telzo2000/cool838ax/img/img00001.jpg

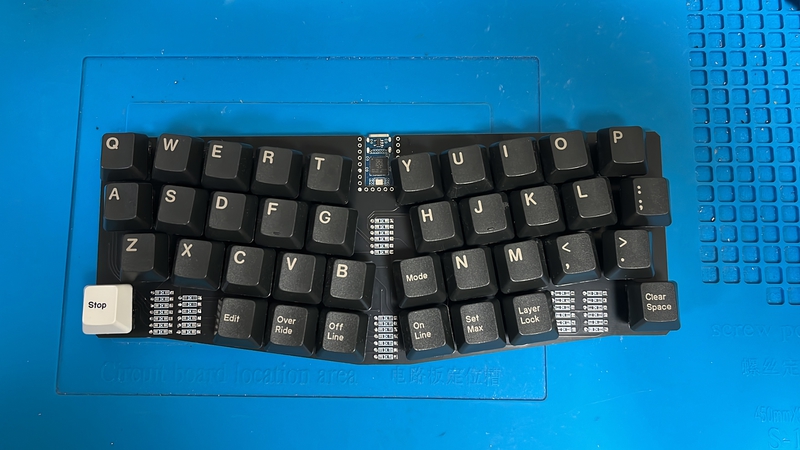
img/img00001.jpg
