telzo2000/cool838ax/img/IMG_1909.jpg

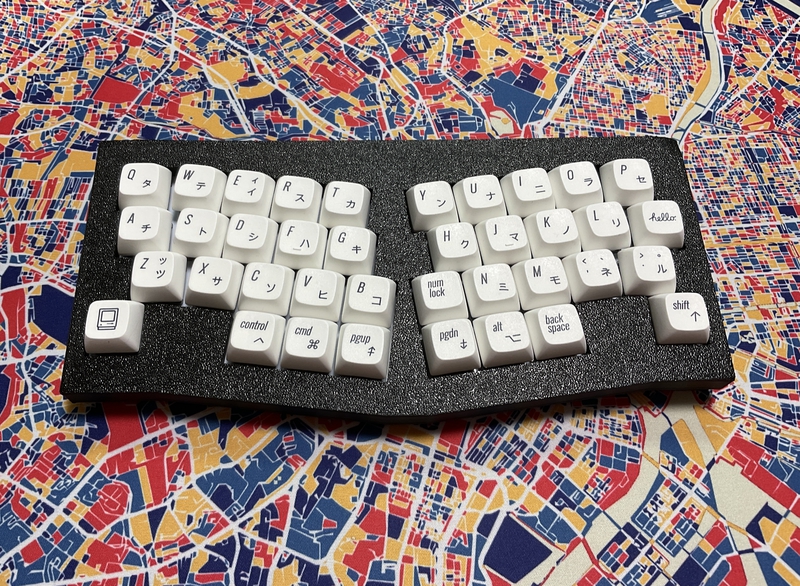
img/IMG_1909.jpg
