telzo2000/cool838ax/img/IMG_1910.jpg

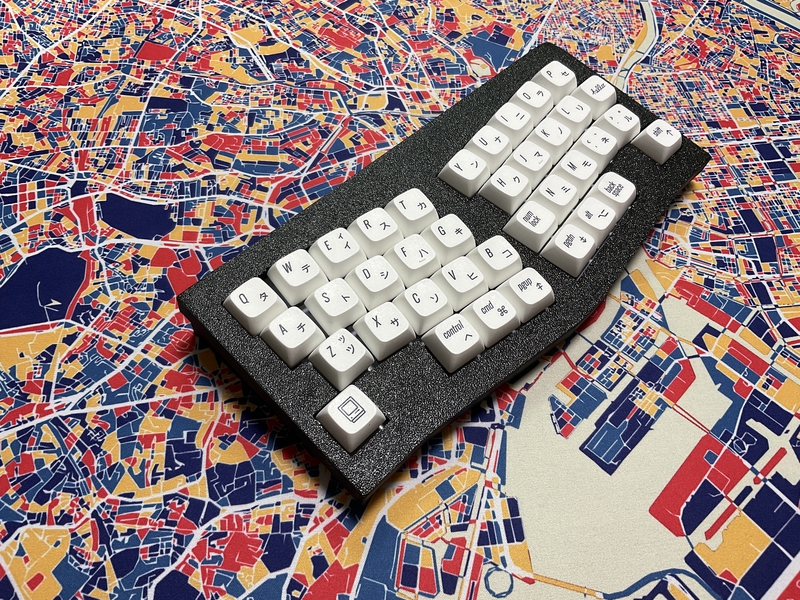
img/IMG_1910.jpg
