telzo2000/cool838ax/img/IMG_1911.jpg

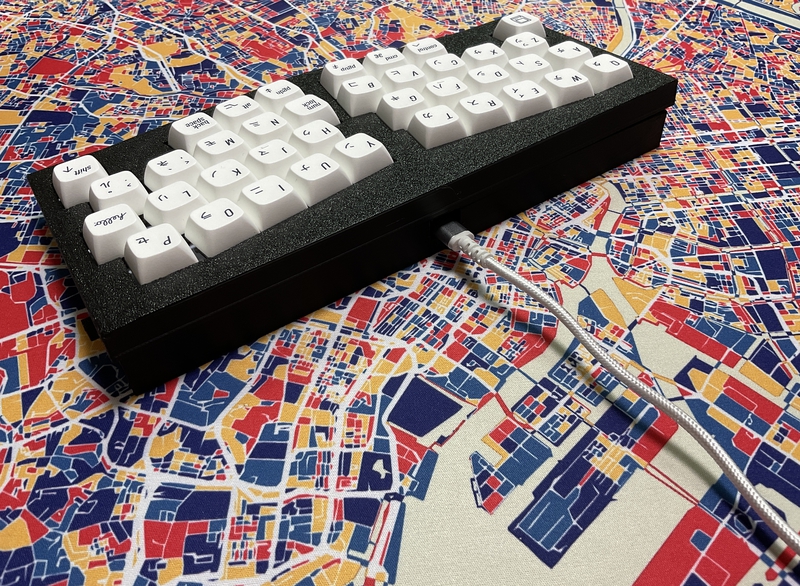
img/IMG_1911.jpg
