telzo2000/cool838ax/img/IMG_1912.jpg

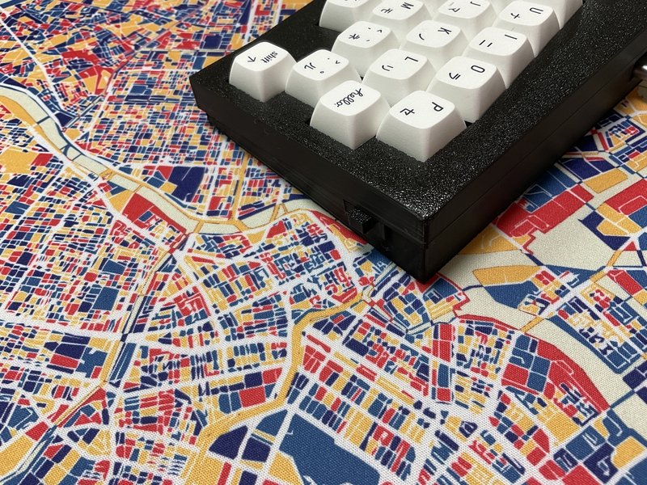
img/IMG_1912.jpg
