telzo2000/cool838ax/img/IMG_1913.jpg

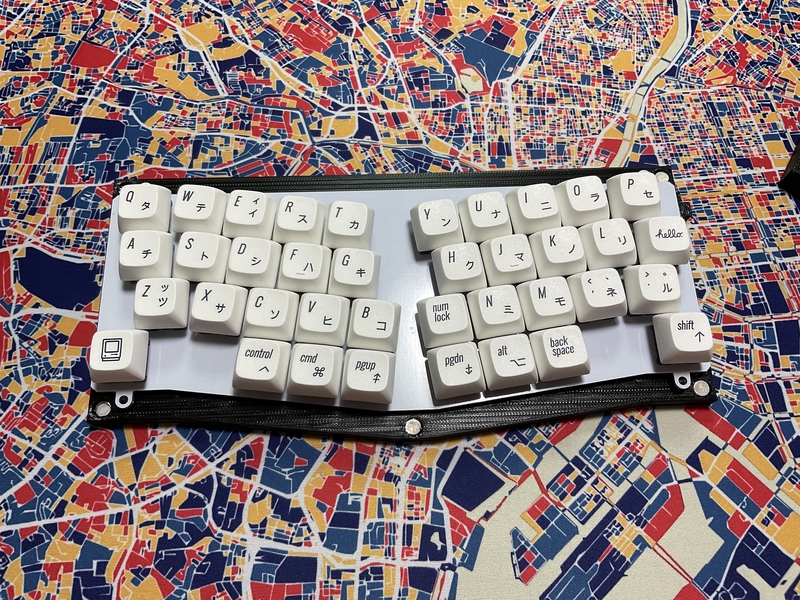
img/IMG_1913.jpg
