telzo2000/cool838ax/img/IMG_1914.jpg

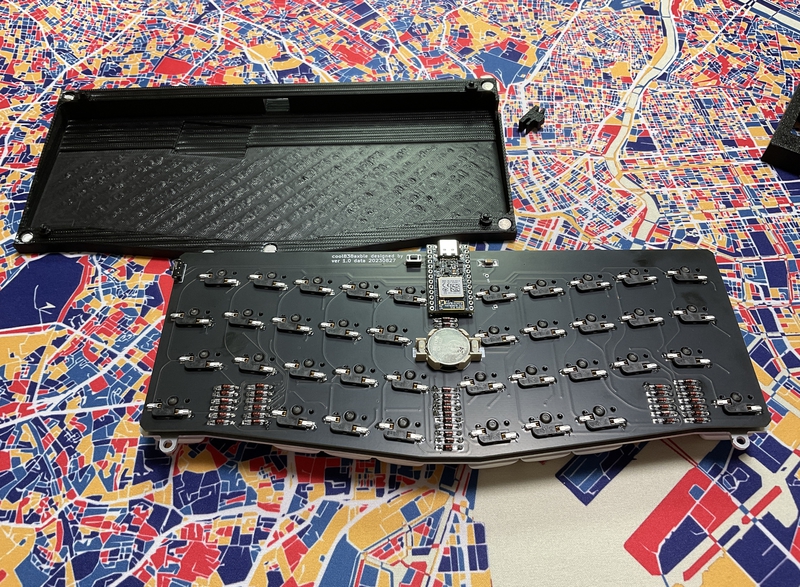
img/IMG_1914.jpg
